HVisMyLife/ExoHand/Exoskeleton/Hand/StickTip.stl

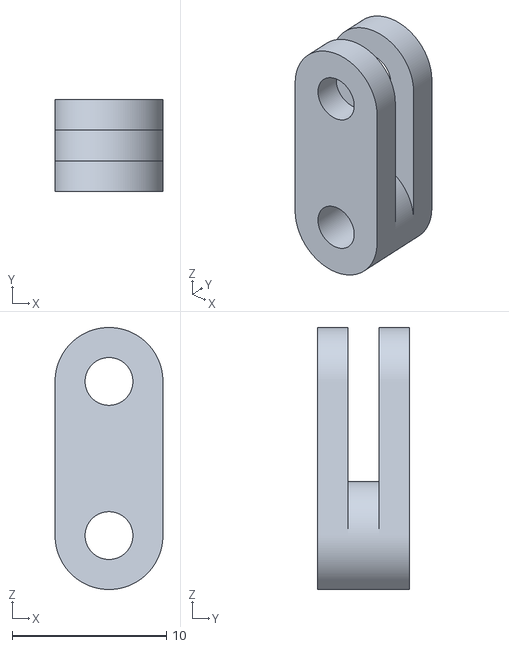
[picture p15: CAD file, 2021-05-07]
Exoskeleton/Hand/StickTip.stl
7.00 x 6.00 x 17.0
