HVisMyLife/ExoHand/Exoskeleton/Arm/Rings/2B.stl

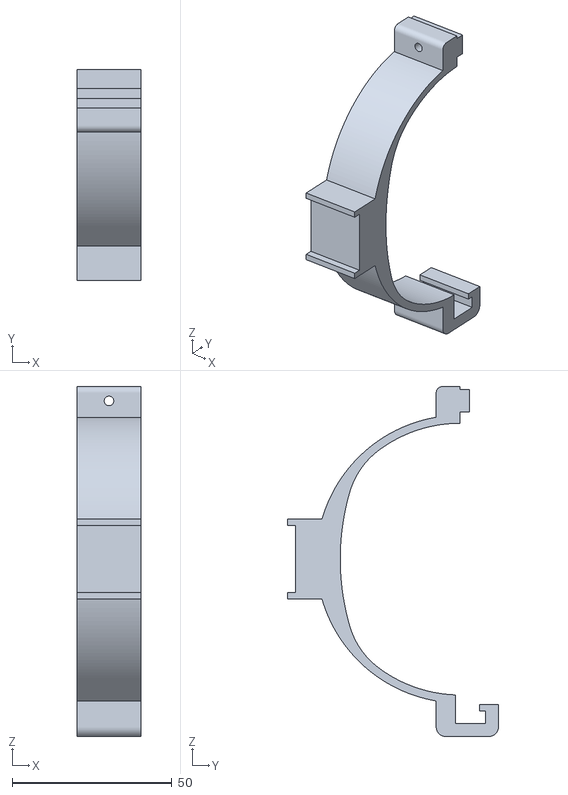
[picture p16: CAD file, 2021-05-07]
Exoskeleton/Arm/Rings/2B.stl
20.0 x 66.0 x 109.5
