HVisMyLife/ExoHand/Exoskeleton/Hand/Rings/20.stl

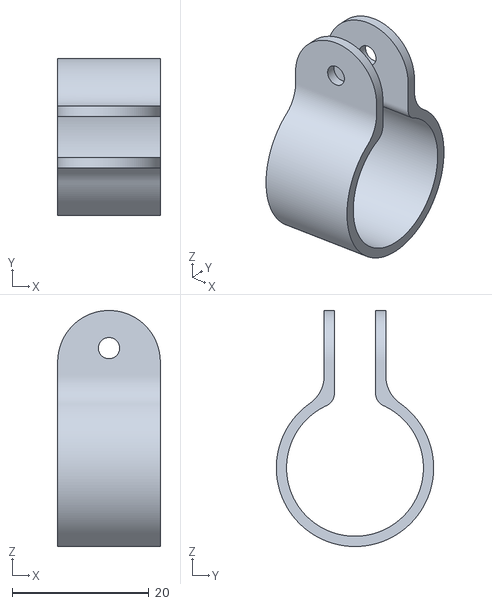
[picture p17: CAD file, 2021-05-07]
Exoskeleton/Hand/Rings/20.stl
15.0 x 23.0 x 34.5
