HVisMyLife/ExoHand/Exoskeleton/Arm/Rings/1B.stl

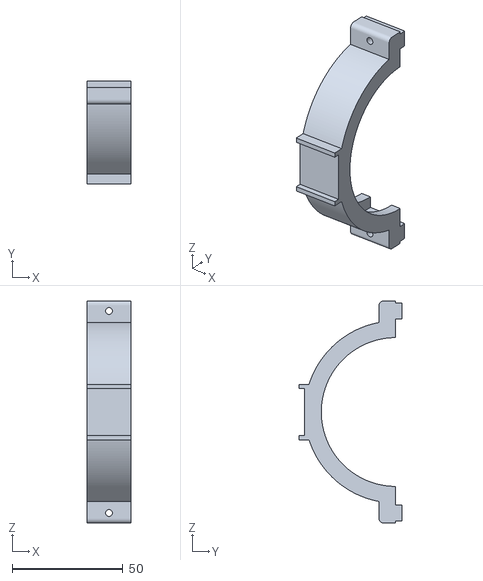
[picture p18: CAD file, 2021-05-07]
Exoskeleton/Arm/Rings/1B.stl
20.0 x 46.5 x 100.0
