HVisMyLife/ExoHand/Exoskeleton/Hand/Rings/14.stl

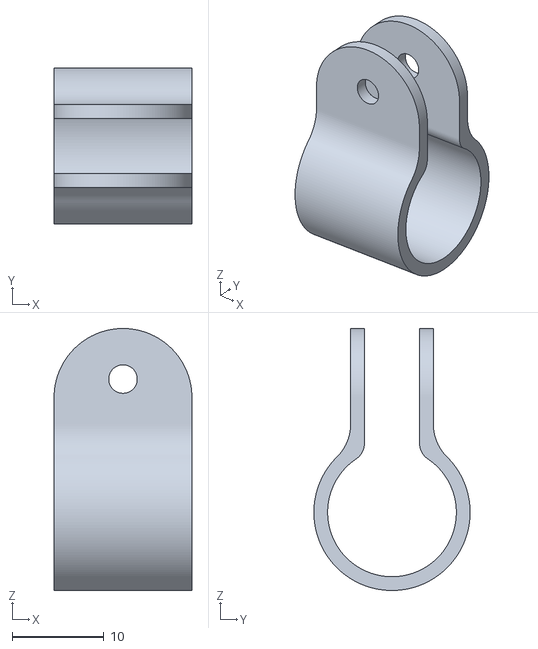
[picture p19: CAD file, 2021-05-07]
Exoskeleton/Hand/Rings/14.stl
15.0 x 17.0 x 28.5
