HVisMyLife/ExoHand/Exoskeleton/Arm/Rings/4A.stl

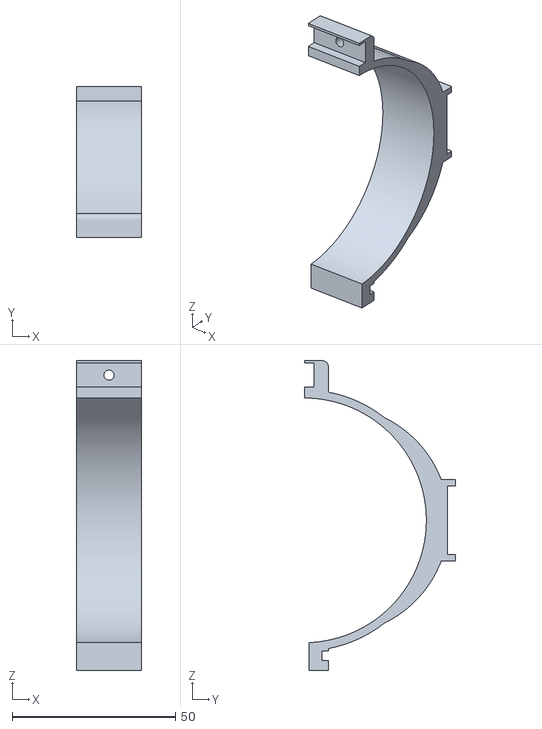
[picture p20: CAD file, 2021-05-07]
Exoskeleton/Arm/Rings/4A.stl
20.0 x 46.4 x 95.0
