HVisMyLife/ExoHand/Exoskeleton/Hand/Rings/15.stl

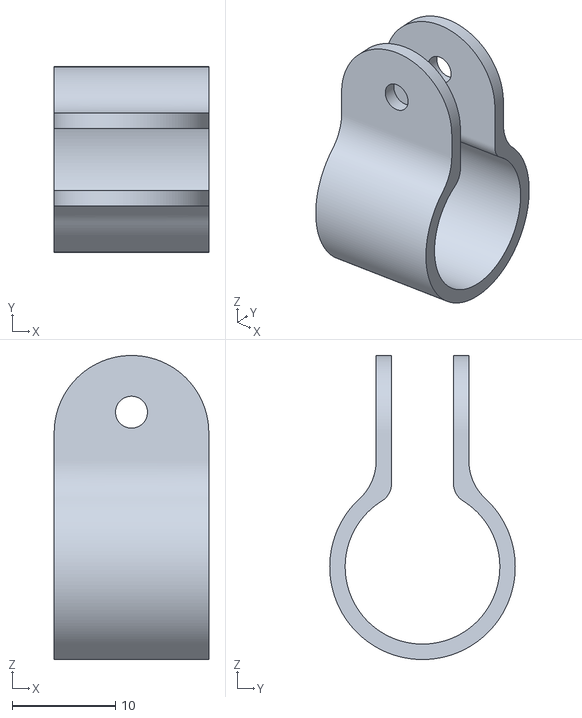
[picture p21: CAD file, 2021-05-07]
Exoskeleton/Hand/Rings/15.stl
15.0 x 18.0 x 29.5
