HVisMyLife/ExoHand/Exoskeleton/Arm/Rings/2A.stl

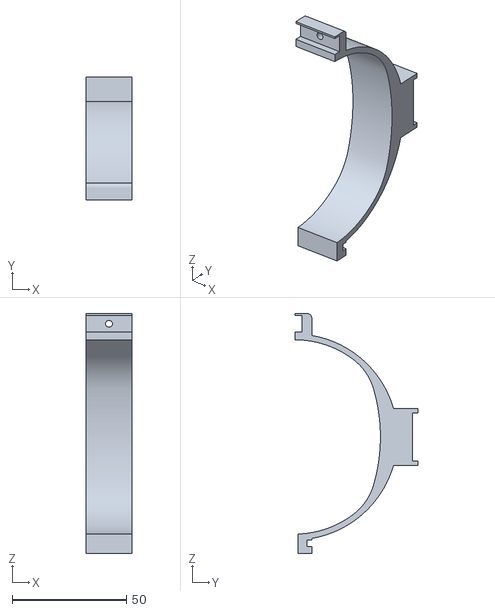
[picture p22: CAD file, 2021-05-07]
Exoskeleton/Arm/Rings/2A.stl
20.0 x 53.9 x 105.0
