HVisMyLife/ExoHand/Exoskeleton/Hand/Rings/19.stl

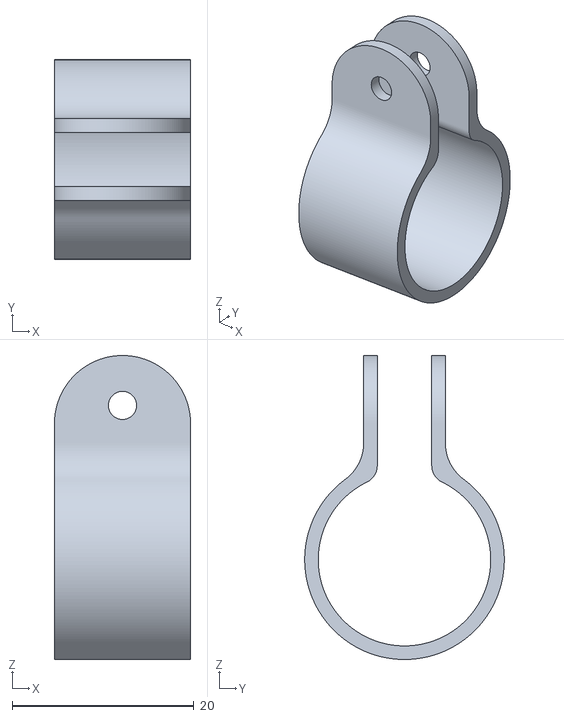
[picture p23: CAD file, 2021-05-07]
Exoskeleton/Hand/Rings/19.stl
15.0 x 22.0 x 33.5
