HVisMyLife/ExoHand/Exoskeleton/Arm/Rings/4B.stl

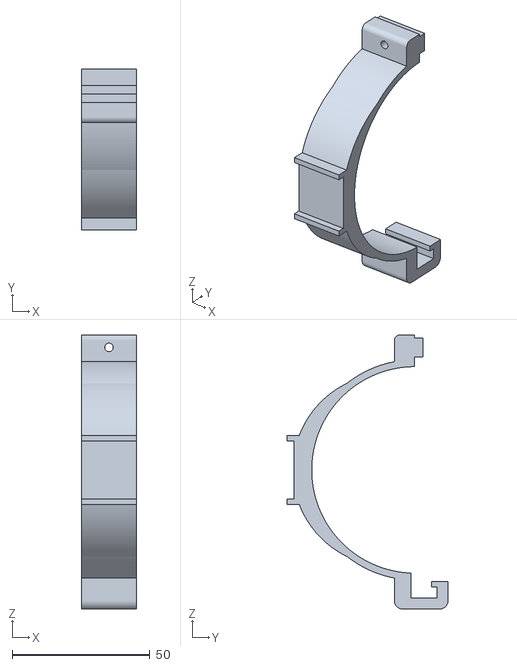
[picture p24: CAD file, 2021-05-07]
Exoskeleton/Arm/Rings/4B.stl
20.0 x 58.5 x 99.5
