HVisMyLife/ExoHand/Exoskeleton/Hand/Rings/16.stl

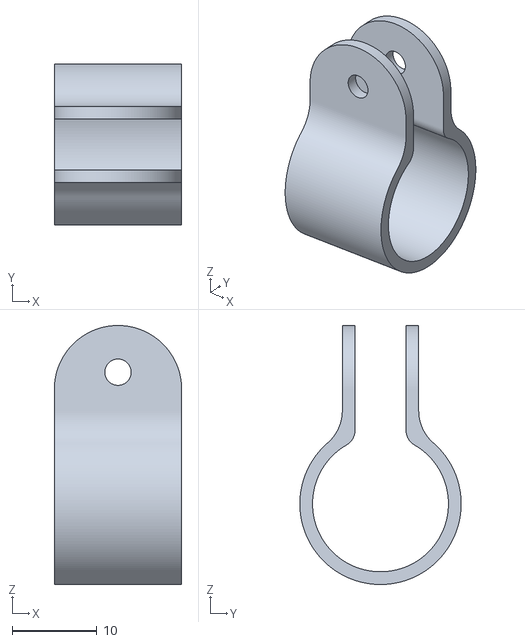
[picture p25: CAD file, 2021-05-07]
Exoskeleton/Hand/Rings/16.stl
15.0 x 19.0 x 30.5
