HVisMyLife/ExoHand/Exoskeleton/Hand/Rings/12.stl

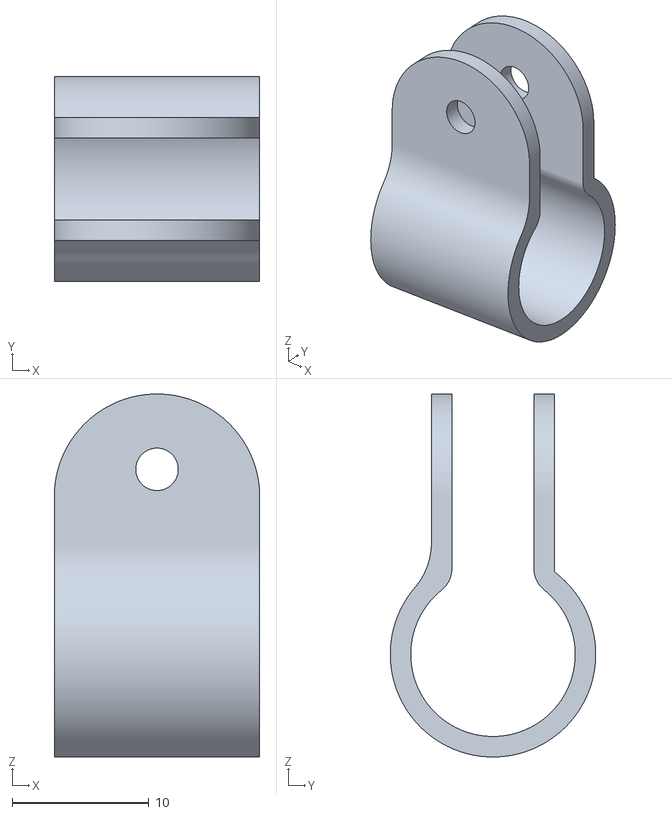
[picture p26: CAD file, 2021-05-07]
Exoskeleton/Hand/Rings/12.stl
15.0 x 15.0 x 26.5
